haricharan39/automatic-colour-weight-sorting-conveyor-belt/Images/WhatsApp Image 2026-05-16 at 14.24.29 (1).jpeg

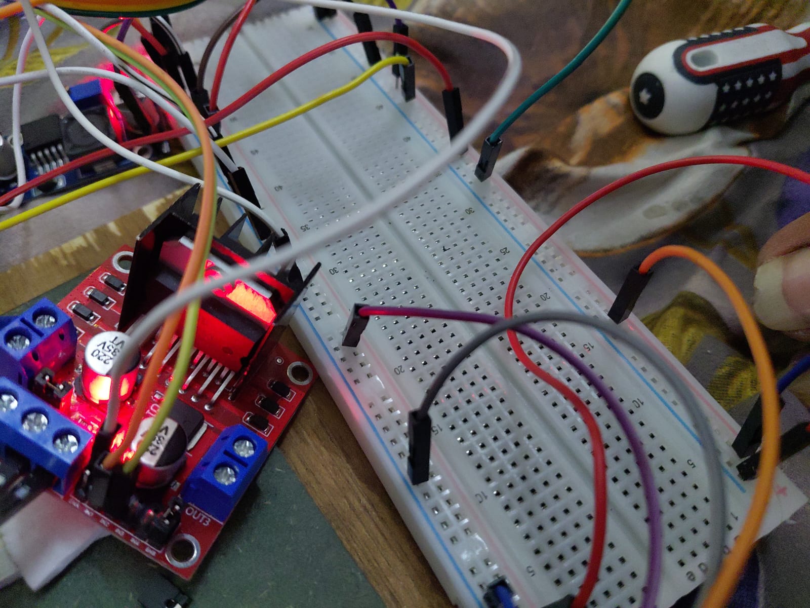
Images/WhatsApp Image 2026-05-16 at 14.24.29 (1).jpeg
