haricharan39/automatic-colour-weight-sorting-conveyor-belt/Images/WhatsApp Image 2026-05-16 at 15.00.24.jpeg

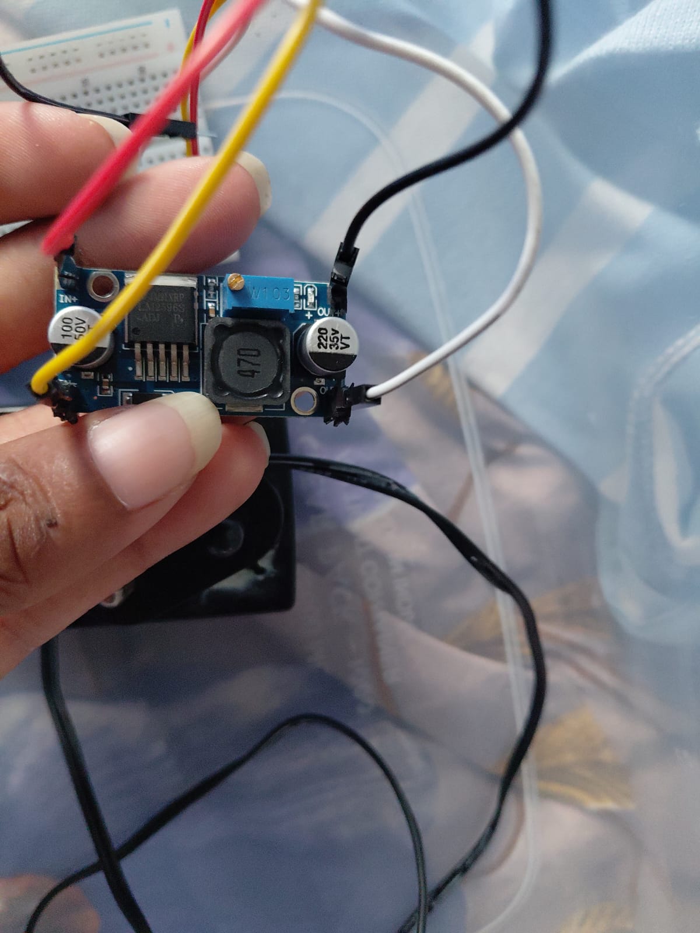
Images/WhatsApp Image 2026-05-16 at 15.00.24.jpeg
